mtroyernl/LoRaWAN-ESP8266/20161231_130729.jpg

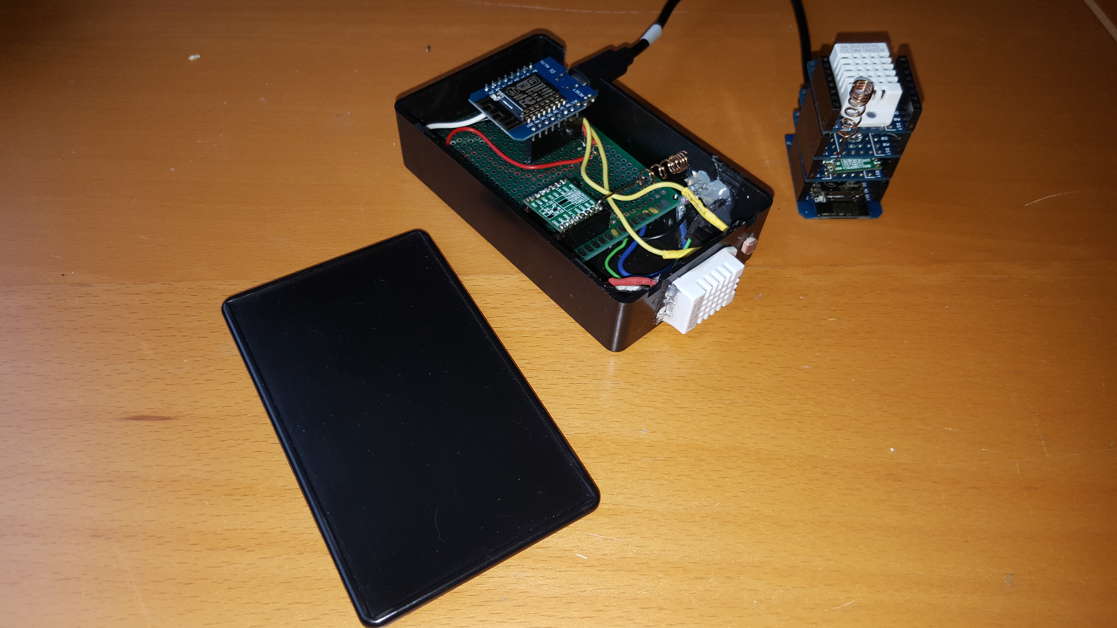
20161231_130729.jpg
