mtroyernl/LoRaWAN-ESP8266/20161231_130917.jpg

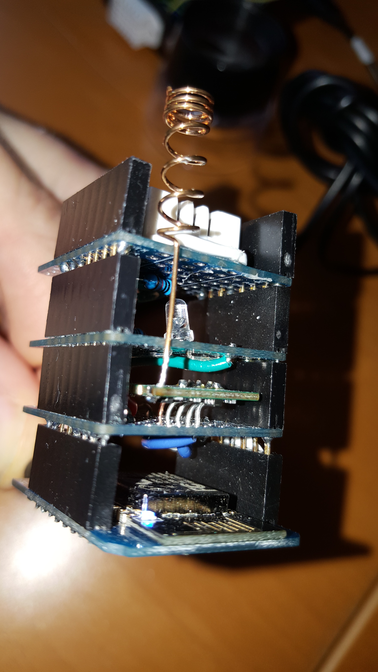
20161231_130917.jpg
